calvin-mcd/NEC-50/Firmware/Source Code/keymaps/vial/config.h

/* SPDX-License-Identifier: GPL-2.0-or-later */

#pragma once

#define VIAL_KEYBOARD_UID {0x6D, 0x4C, 0x97, 0x54, 0x8B, 0xBE, 0x71, 0x77}

/* CONSIDER ADDING AN UNLOCK COMBO. SEE DOCUMENTATION. */
#define VIAL_INSECURE
